fablab-chaux-de-fonds/martilab/images/fablab.png

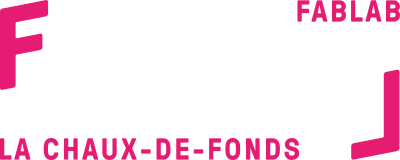
images/fablab.png
